piermatt/openspinnr/ver_B/stl_files/motor-holder_collector.stl

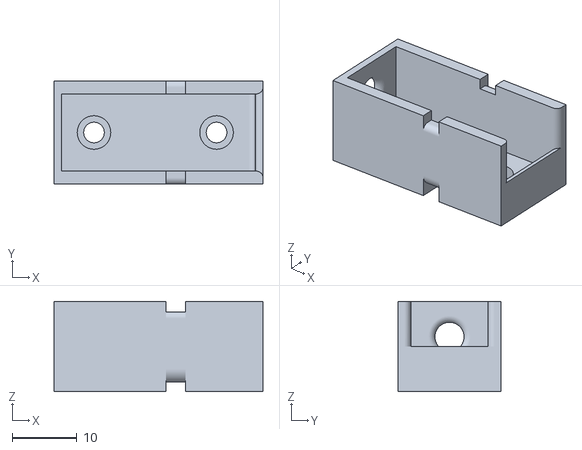
[picture p16: CAD file, 2021-07-28]
ver_B/stl_files/motor-holder_collector.stl
32.4 x 16.0 x 14.0
