piermatt/openspinnr/ver_A/sketches/5E.FCStd

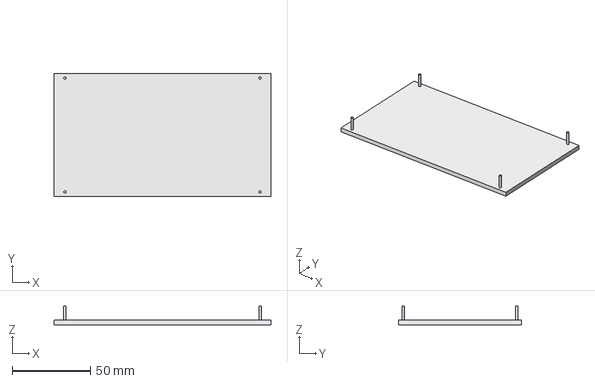
[picture p17: CAD file, 2021-07-28, an earlier design]
ver_A/sketches/5E.FCStd
139.0 x 79.0 x 12.0 mm
