piermatt/openspinnr/ver_A/sketches/1D.FCStd

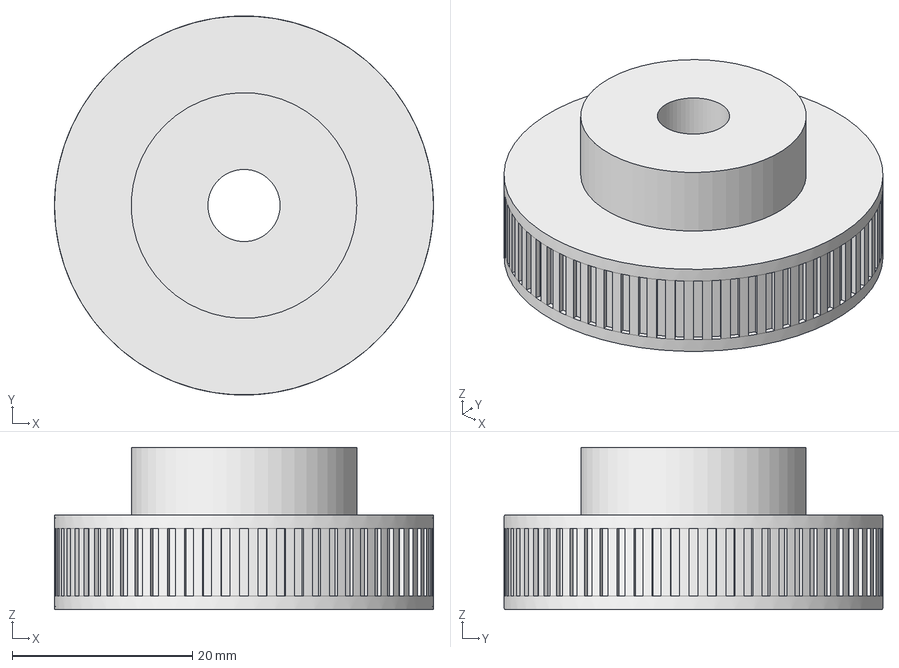
[picture p18: CAD file, 2021-07-28, an earlier design]
ver_A/sketches/1D.FCStd
42.0 x 42.0 x 18.0 mm
