piermatt/openspinnr/ver_A/sketches/5B.FCStd

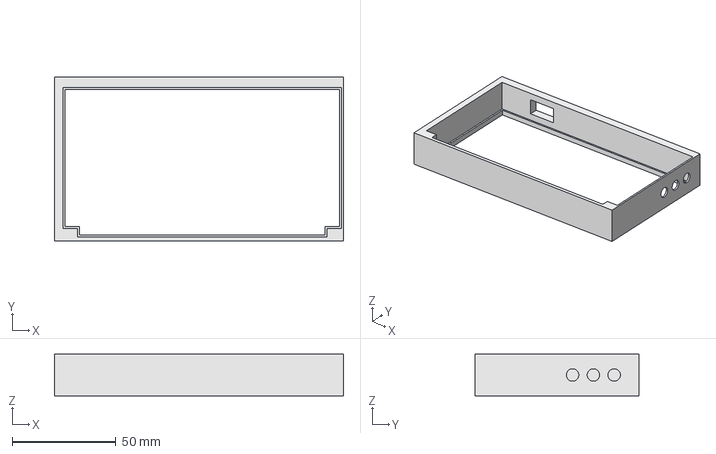
[picture p19: CAD file, 2021-07-28, an earlier design]
ver_A/sketches/5B.FCStd
139.0 x 79.0 x 20.0 mm
